DamonHolland/RubiksRobot/3D_Files/Final_3D_Files_Print_These/PS/PowerStruct.3mf

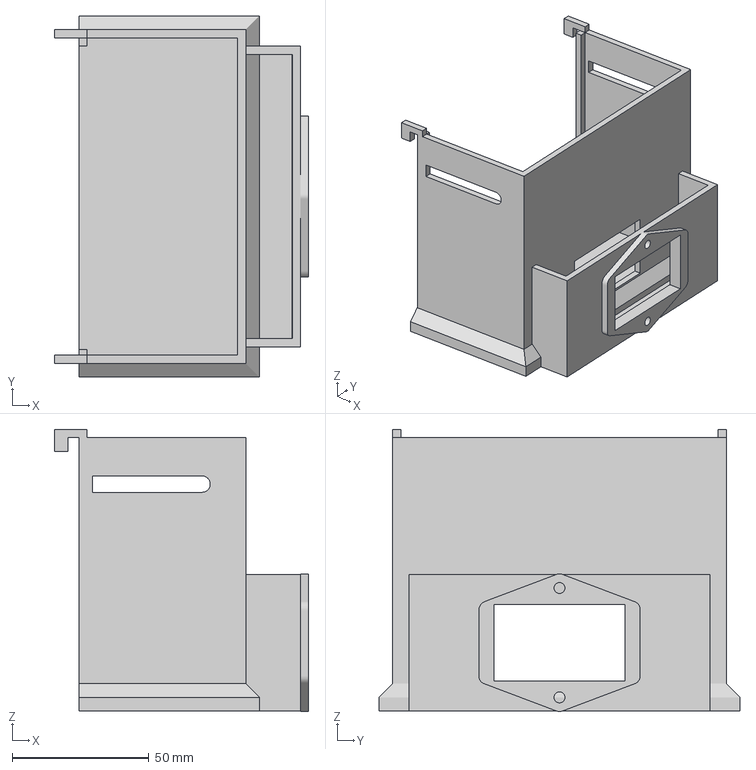
[picture p21: CAD file, 2022-01-24]
3D_Files/Final_3D_Files_Print_These/PS/PowerStruct.3mf
93.0 x 132.0 x 103.2 mm
