DamonHolland/RubiksRobot/3D_Files/NewArm/cubeThing.3mf

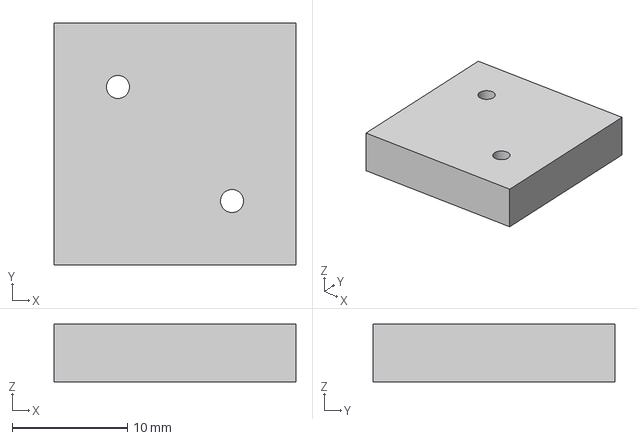
[picture p22: CAD file, 2022-01-30]
3D_Files/NewArm/cubeThing.3mf
21.0 x 21.0 x 5.00 mm
