DamonHolland/RubiksRobot/3D_Files/NewConnectors/BackConnector.3mf

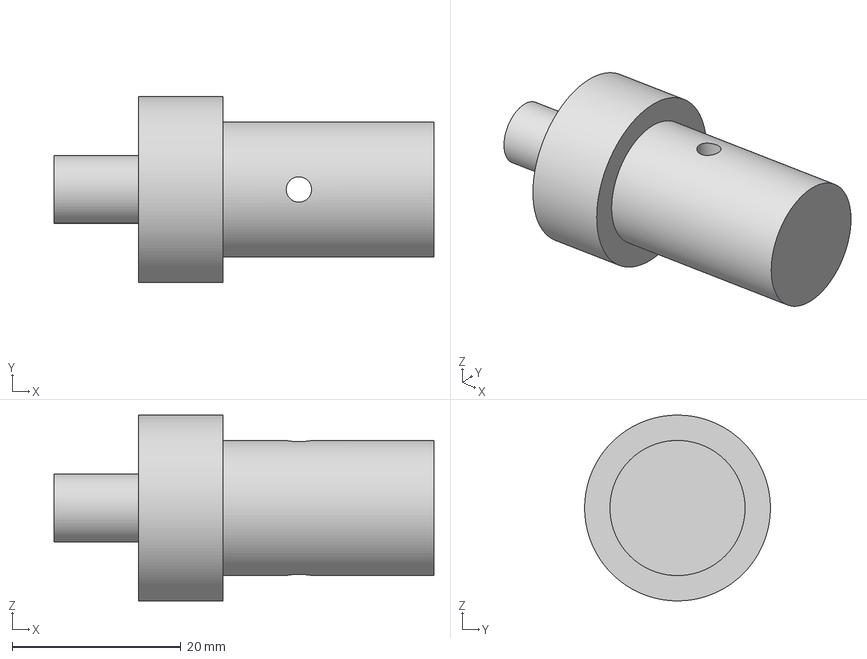
[picture p23: CAD file, 2021-12-20]
3D_Files/NewConnectors/BackConnector.3mf
45.0 x 22.0 x 22.0 mm
