DamonHolland/RubiksRobot/3D_Files/Structure/LowerHolder.3mf

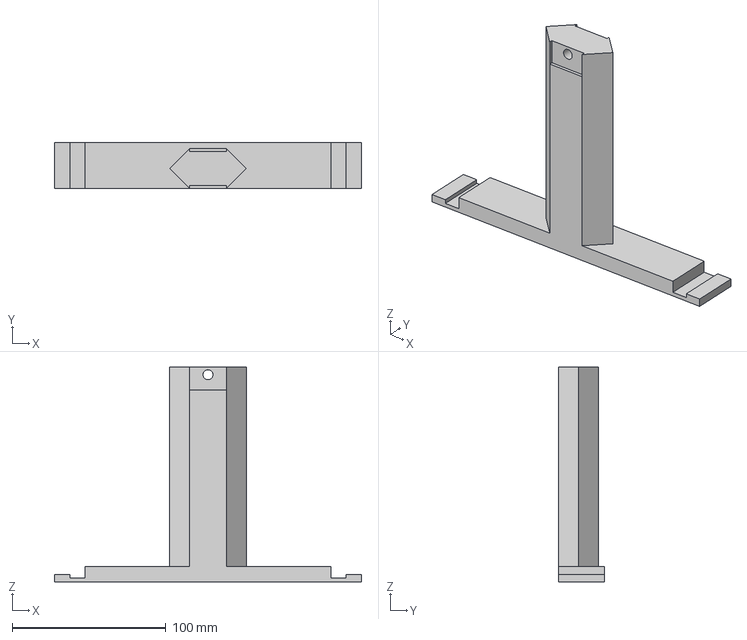
[picture p24: CAD file, 2021-11-13]
3D_Files/Structure/LowerHolder.3mf
200.0 x 30.0 x 140.0 mm
