DamonHolland/RubiksRobot/3D_Files/3DFiles/OutConnectorPin.3mf

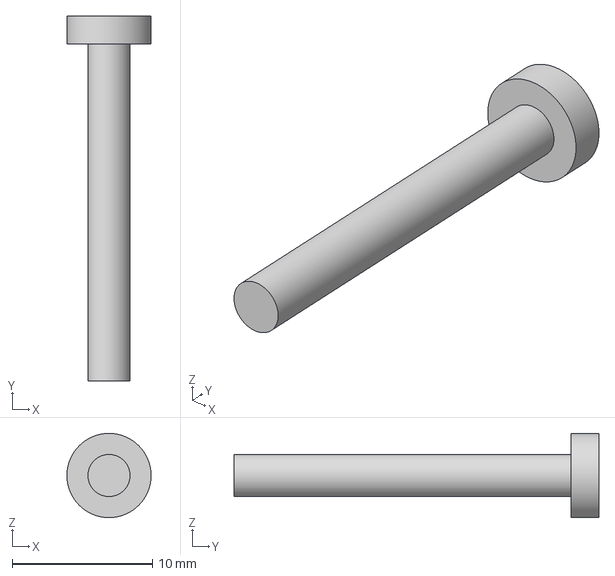
[picture p25: CAD file, 2021-11-19]
3D_Files/3DFiles/OutConnectorPin.3mf
6.00 x 26.0 x 6.00 mm
