DamonHolland/RubiksRobot/3D_Files/Final_3D_Files_Print_These/Arm/Outter.3mf

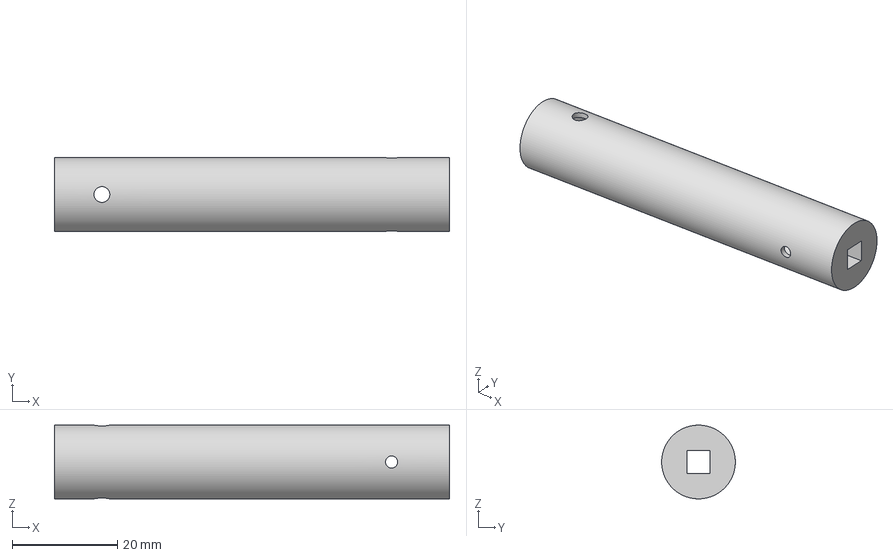
[picture p26: CAD file, 2022-01-17]
3D_Files/Final_3D_Files_Print_These/Arm/Outter.3mf
75.0 x 14.0 x 14.0 mm
