DamonHolland/RubiksRobot/3D_Files/Final_3D_Files_Print_These/BottomFrame/CornerLower.3mf

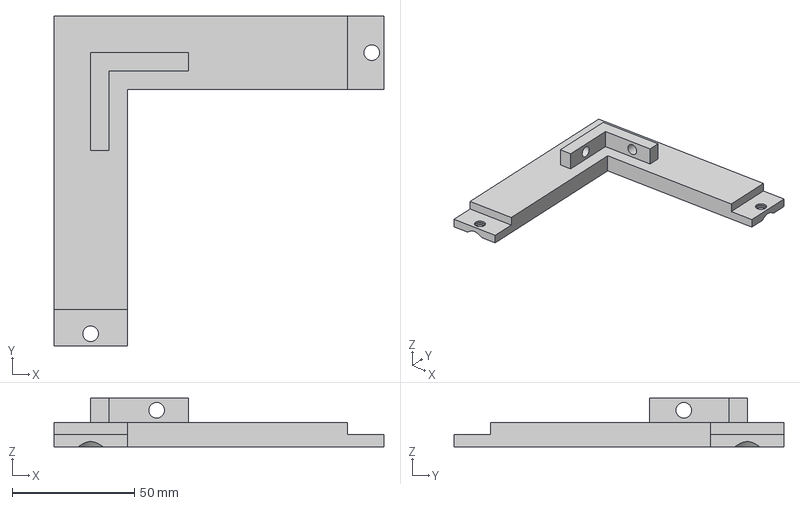
[picture p27: CAD file, 2021-12-20]
3D_Files/Final_3D_Files_Print_These/BottomFrame/CornerLower.3mf
135.0 x 135.0 x 20.0 mm
