DamonHolland/RubiksRobot/3D_Files/Final_3D_Files_Print_These/PS/DriverStruct.3mf

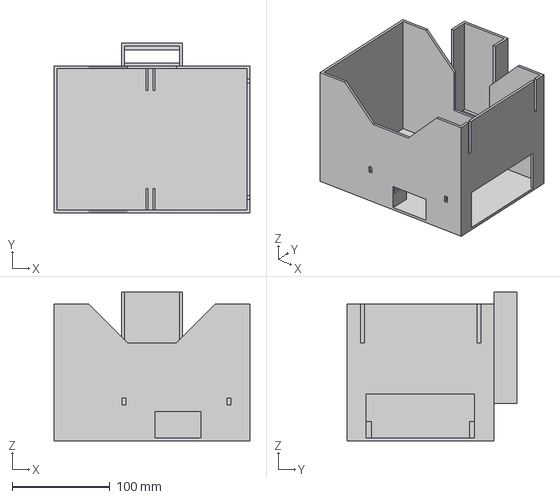
[picture p28: CAD file, 2022-01-08]
3D_Files/Final_3D_Files_Print_These/PS/DriverStruct.3mf
200.0 x 173.0 x 152.0 mm
