DamonHolland/RubiksRobot/3D_Files/Front_Arm.stl

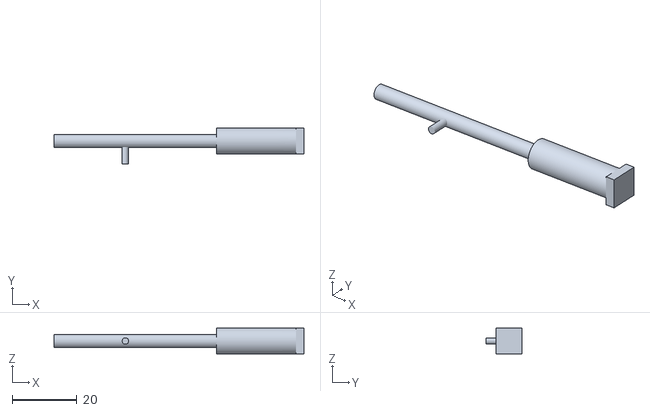
[picture p29: CAD file, 2021-11-13]
3D_Files/Front_Arm.stl
77.0 x 11.0 x 8.00
