DamonHolland/RubiksRobot/3D_Files/Structure/UpperHolder.3mf

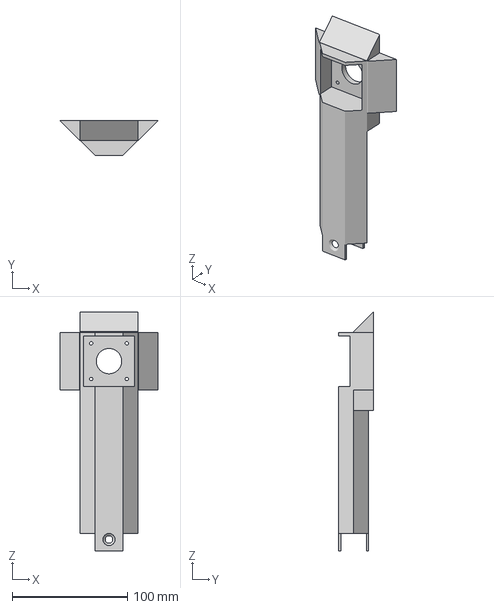
[picture p30: CAD file, 2021-11-13]
3D_Files/Structure/UpperHolder.3mf
85.4 x 30.0 x 207.7 mm
