DamonHolland/RubiksRobot/3D_Files/3DFiles/CleanConnector.3mf

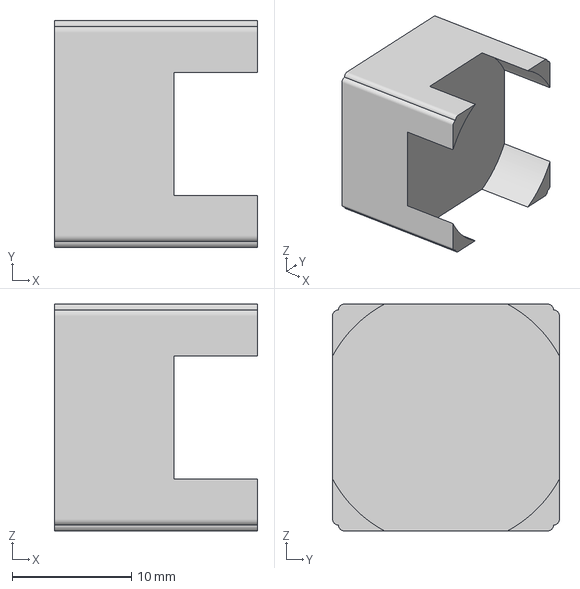
[picture p31: CAD file, 2021-11-17]
3D_Files/3DFiles/CleanConnector.3mf
17.0 x 19.0 x 19.0 mm
