DamonHolland/RubiksRobot/3D_Files/Final_3D_Files_Print_These/Arm/pin.3mf

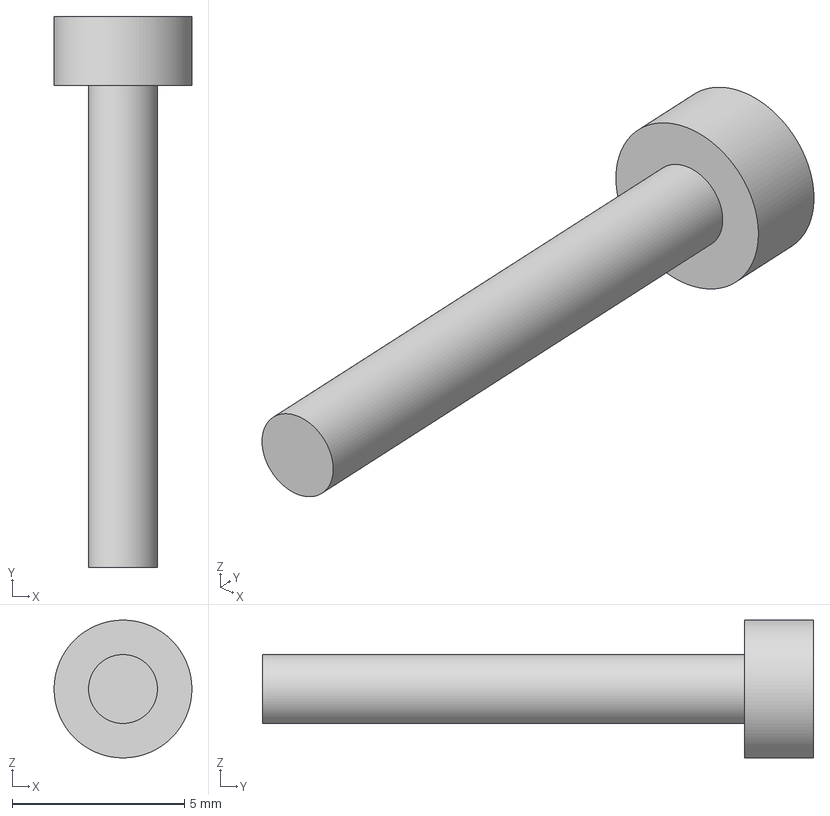
[picture p32: CAD file, 2022-01-17]
3D_Files/Final_3D_Files_Print_These/Arm/pin.3mf
4.00 x 16.0 x 4.00 mm
