DamonHolland/RubiksRobot/3D_Files/Final_3D_Files_Print_These/PS/WireStruct.3mf

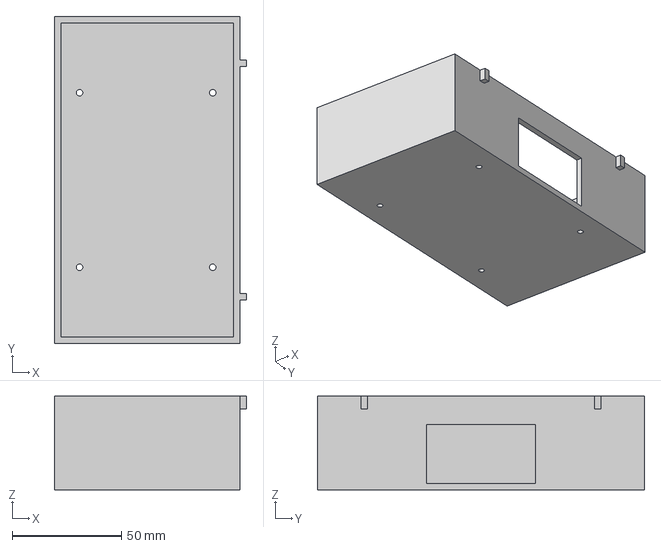
[picture p33: CAD file, 2022-01-08]
3D_Files/Final_3D_Files_Print_These/PS/WireStruct.3mf
88.0 x 150.0 x 43.0 mm
