DamonHolland/RubiksRobot/3D_Files/Structure/CorrectPin.3mf

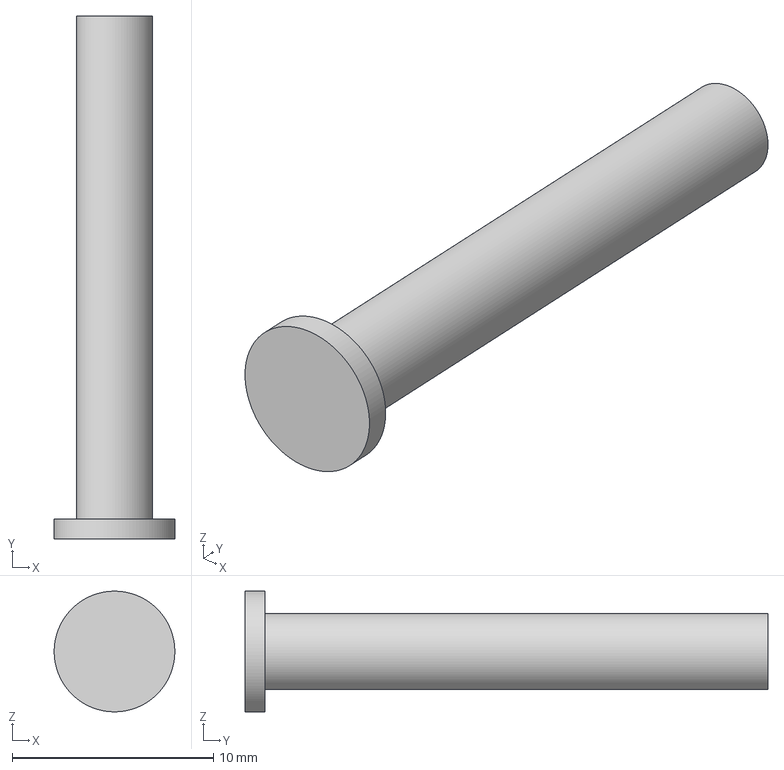
[picture p34: CAD file, 2021-11-13]
3D_Files/Structure/CorrectPin.3mf
6.00 x 26.0 x 6.00 mm
