DamonHolland/RubiksRobot/3D_Files/3DFiles/InnerConnectorHole.3mf

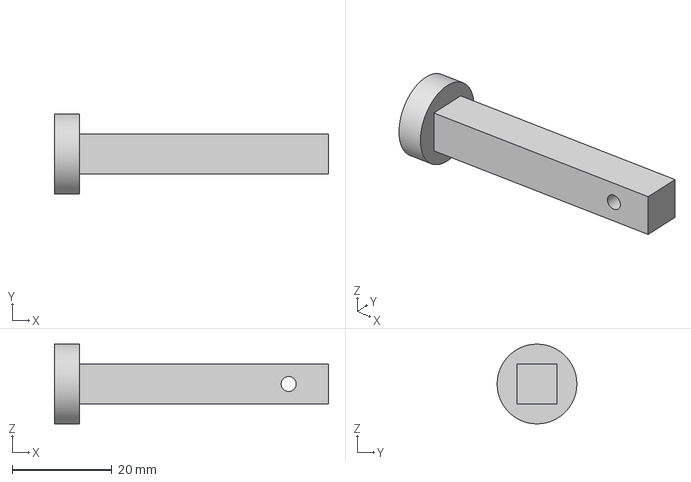
[picture p35: CAD file, 2021-11-16]
3D_Files/3DFiles/InnerConnectorHole.3mf
55.0 x 16.0 x 16.0 mm
