DamonHolland/RubiksRobot/3D_Files/Final_3D_Files_Print_These/Arm/Back.3mf

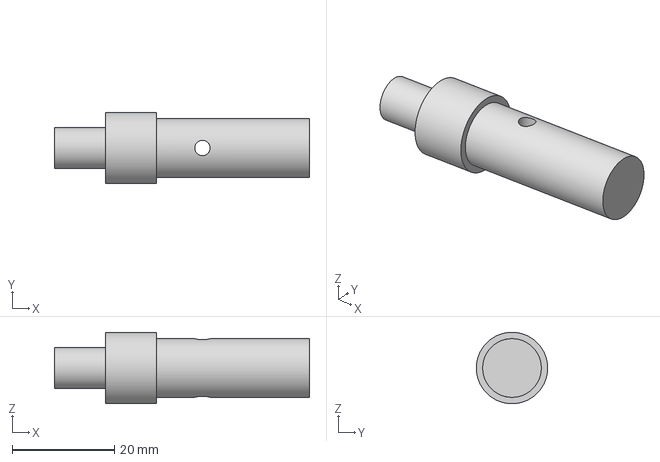
[picture p36: CAD file, 2022-01-17]
3D_Files/Final_3D_Files_Print_These/Arm/Back.3mf
50.0 x 14.0 x 14.0 mm
