DamonHolland/RubiksRobot/3D_Files/Final_3D_Files_Print_These/BottomFrame/BottomStructure.3mf

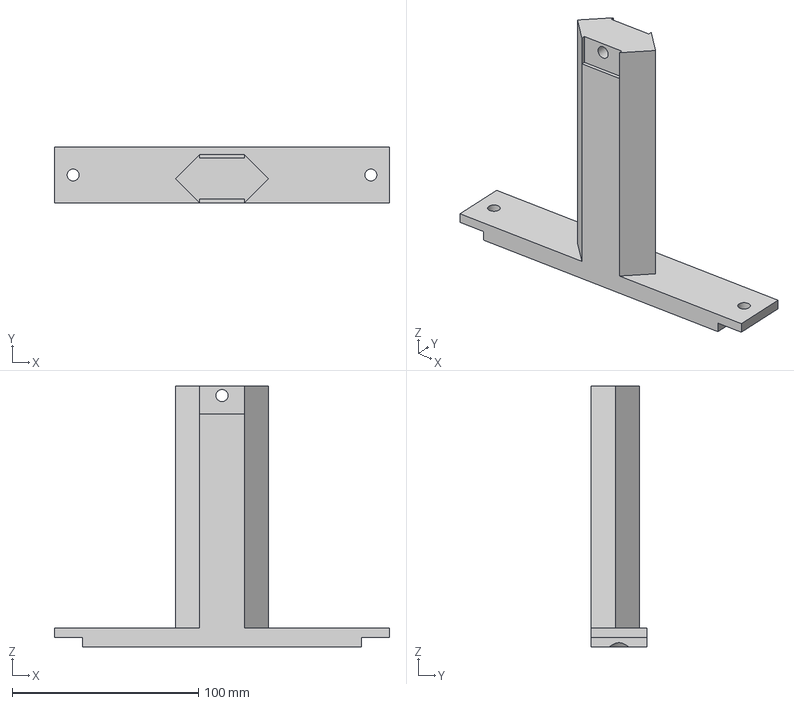
[picture p37: CAD file, 2021-11-13]
3D_Files/Final_3D_Files_Print_These/BottomFrame/BottomStructure.3mf
180.0 x 30.0 x 140.0 mm
