DamonHolland/RubiksRobot/3D_Files/Final_3D_Files_Print_These/CircleFrame/SideCircle2.3mf

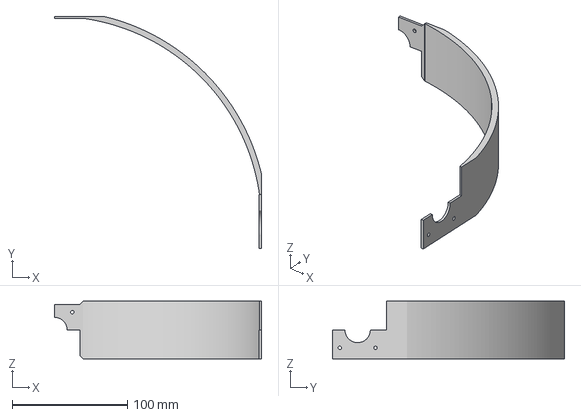
[picture p38: CAD file, 2021-11-13]
3D_Files/Final_3D_Files_Print_These/CircleFrame/SideCircle2.3mf
180.0 x 202.0 x 50.0 mm
