DamonHolland/RubiksRobot/3D_Files/Final_3D_Files_Print_These/PS/handle.3mf

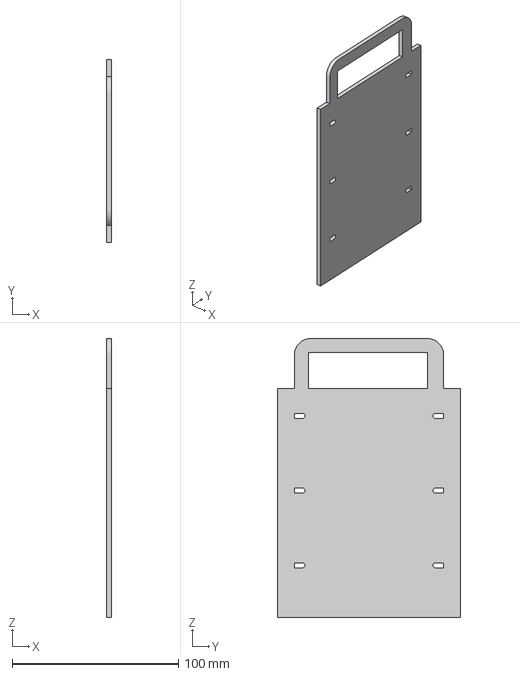
[picture p39: CAD file, 2022-01-05]
3D_Files/Final_3D_Files_Print_These/PS/handle.3mf
3.00 x 110.0 x 168.0 mm
