DamonHolland/RubiksRobot/3D_Files/3DFiles/FinalConnectorLong.3mf

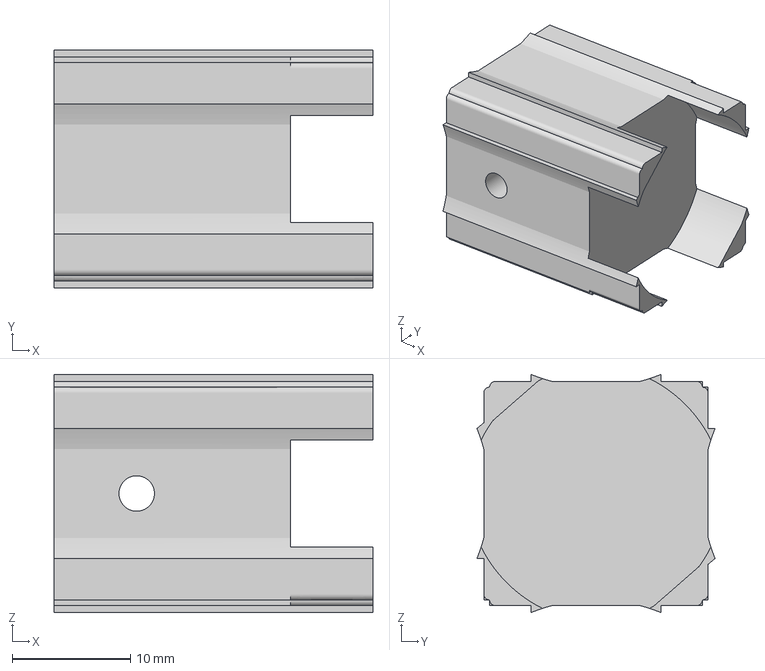
[picture p40: CAD file, 2021-11-16]
3D_Files/3DFiles/FinalConnectorLong.3mf
27.0 x 20.2 x 20.2 mm
