DamonHolland/RubiksRobot/3D_Files/Final_3D_Files_Print_These/BottomFrame/2ConnectorTop.3mf

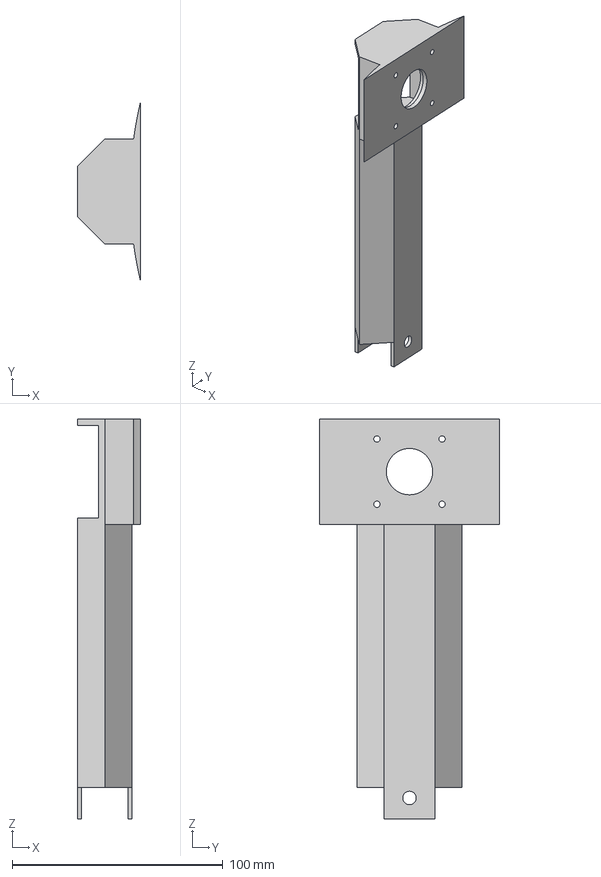
[picture p41: CAD file, 2021-11-13]
3D_Files/Final_3D_Files_Print_These/BottomFrame/2ConnectorTop.3mf
30.0 x 85.4 x 190.0 mm
