DamonHolland/RubiksRobot/3D_Files/3DFiles/FinalConnectorBest.3mf

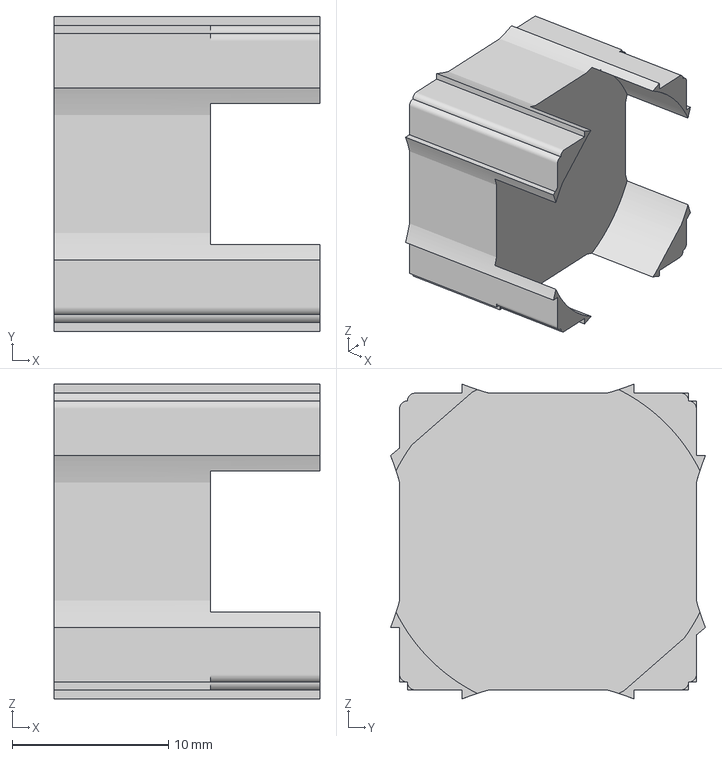
[picture p42: CAD file, 2021-11-16]
3D_Files/3DFiles/FinalConnectorBest.3mf
17.0 x 20.2 x 20.2 mm
