DamonHolland/RubiksRobot/3D_Files/Final_3D_Files_Print_These/BottomFrame/CornerLowerNoConnector.3mf

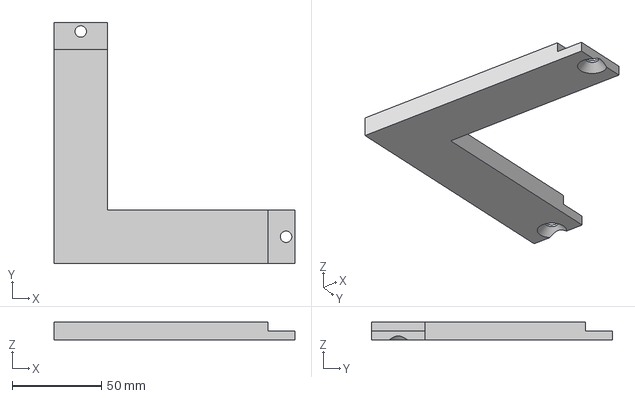
[picture p43: CAD file, 2021-11-13]
3D_Files/Final_3D_Files_Print_These/BottomFrame/CornerLowerNoConnector.3mf
135.0 x 135.0 x 10.0 mm
