DamonHolland/RubiksRobot/3D_Files/3DFiles/BigFinalConnector.3mf

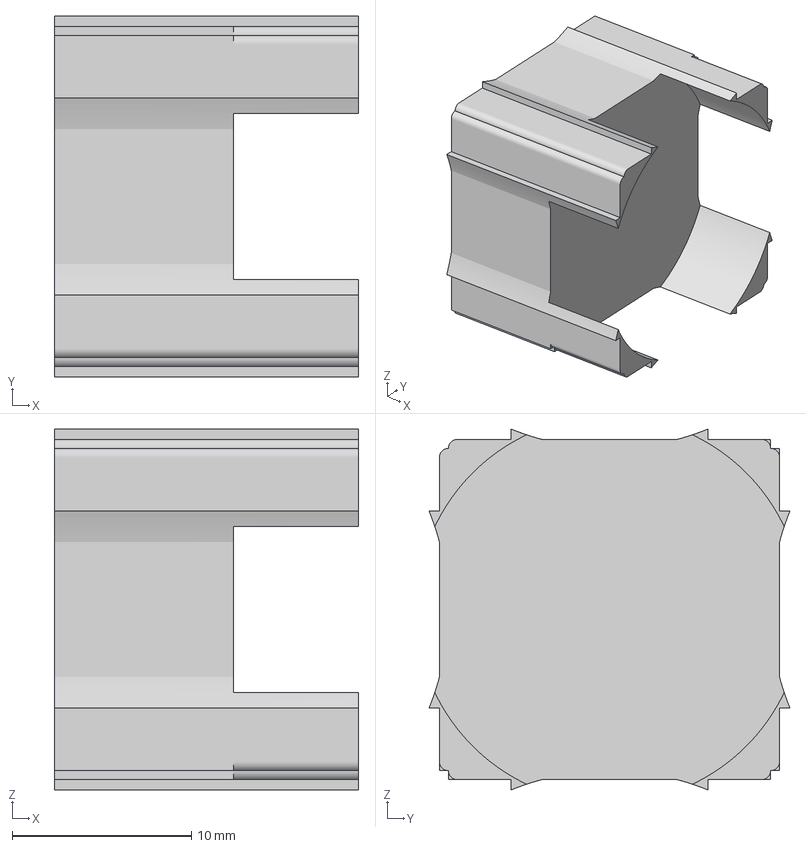
[picture p44: CAD file, 2021-11-15]
3D_Files/3DFiles/BigFinalConnector.3mf
17.0 x 20.2 x 20.2 mm
