DamonHolland/RubiksRobot/3D_Files/3DFiles/TallCamMiddle.3mf

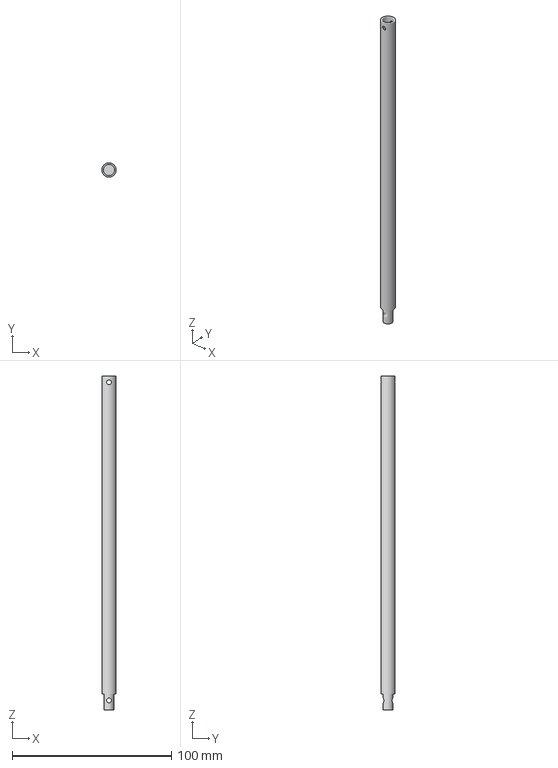
[picture p45: CAD file, 2021-11-14]
3D_Files/3DFiles/TallCamMiddle.3mf
9.00 x 9.00 x 210.0 mm
