DamonHolland/RubiksRobot/3D_Files/3DFiles/TallCamLower.3mf

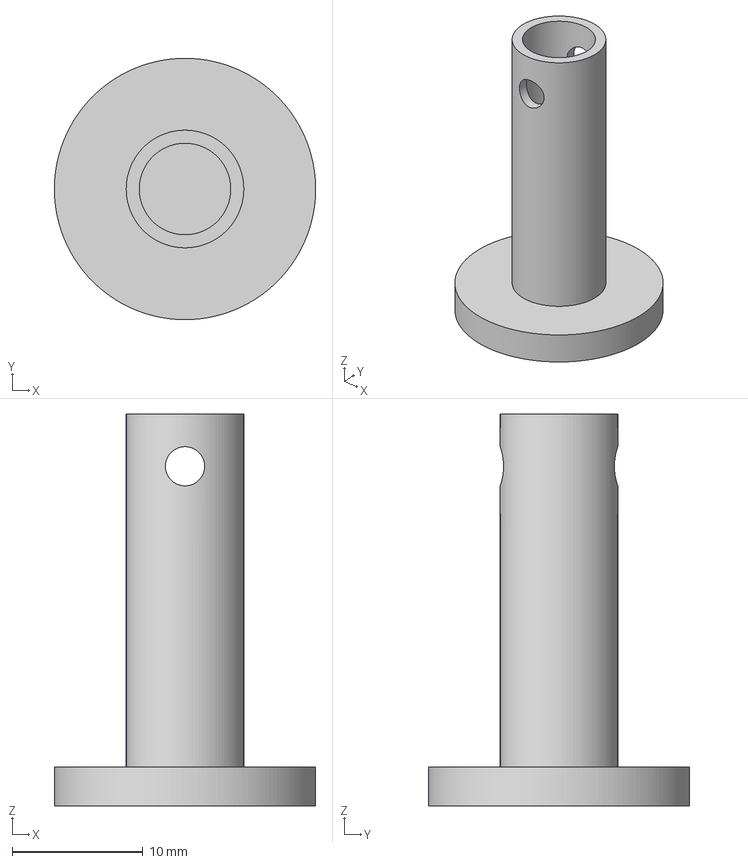
[picture p46: CAD file, 2021-11-14]
3D_Files/3DFiles/TallCamLower.3mf
20.0 x 20.0 x 30.0 mm
