DamonHolland/RubiksRobot/3D_Files/3DFiles/TallCamUpper.3mf

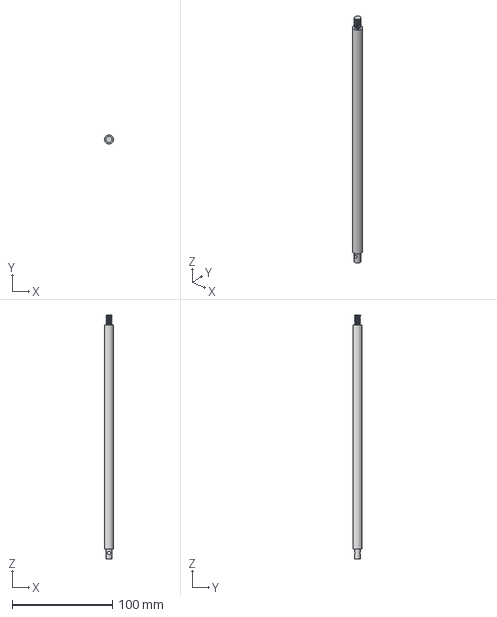
[picture p47: CAD file, 2021-11-13]
3D_Files/3DFiles/TallCamUpper.3mf
8.99 x 8.99 x 243.0 mm
