DamonHolland/RubiksRobot/3D_Files/3DFiles/NewCornerWithHole.3mf

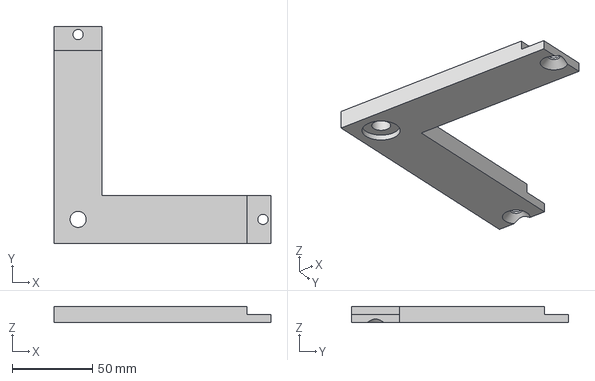
[picture p48: CAD file, 2021-11-13]
3D_Files/3DFiles/NewCornerWithHole.3mf
135.0 x 135.0 x 10.0 mm
