DamonHolland/RubiksRobot/3D_Files/3DFiles/NewBackConnector.3mf

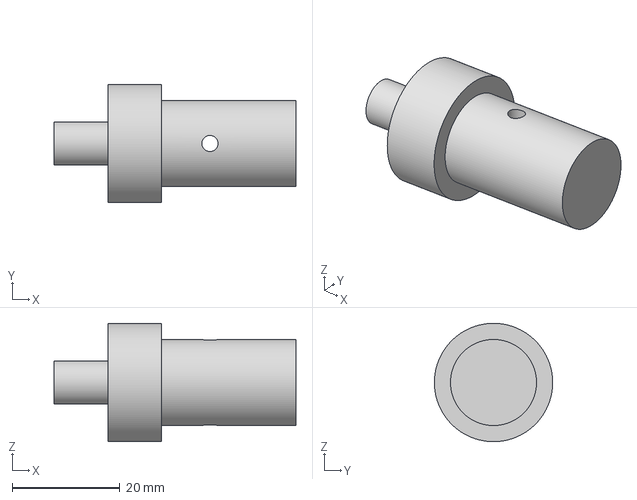
[picture p49: CAD file, 2021-11-13]
3D_Files/3DFiles/NewBackConnector.3mf
45.0 x 22.0 x 22.0 mm
