DamonHolland/RubiksRobot/3D_Files/3DFiles/PillarSmall.3mf

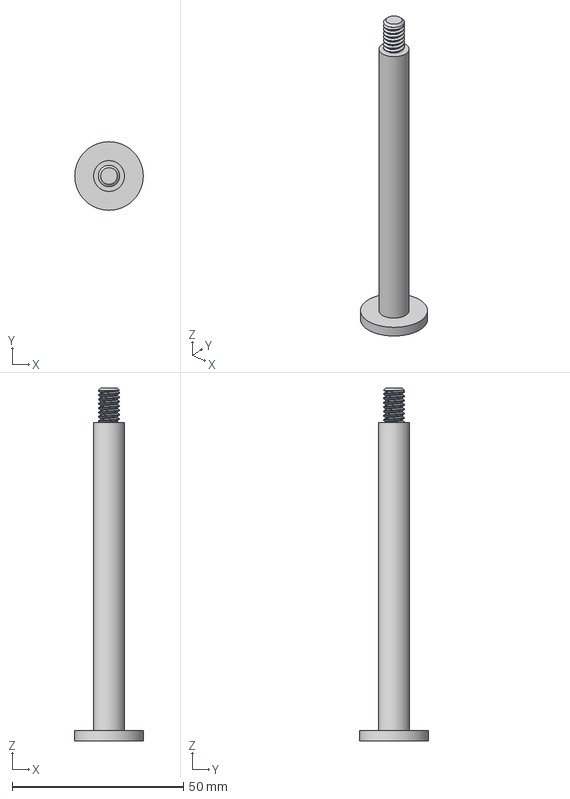
[picture p50: CAD file, 2021-11-13]
3D_Files/3DFiles/PillarSmall.3mf
20.0 x 20.0 x 103.0 mm
