DamonHolland/RubiksRobot/3D_Files/3DFiles/NewestConnector.3mf

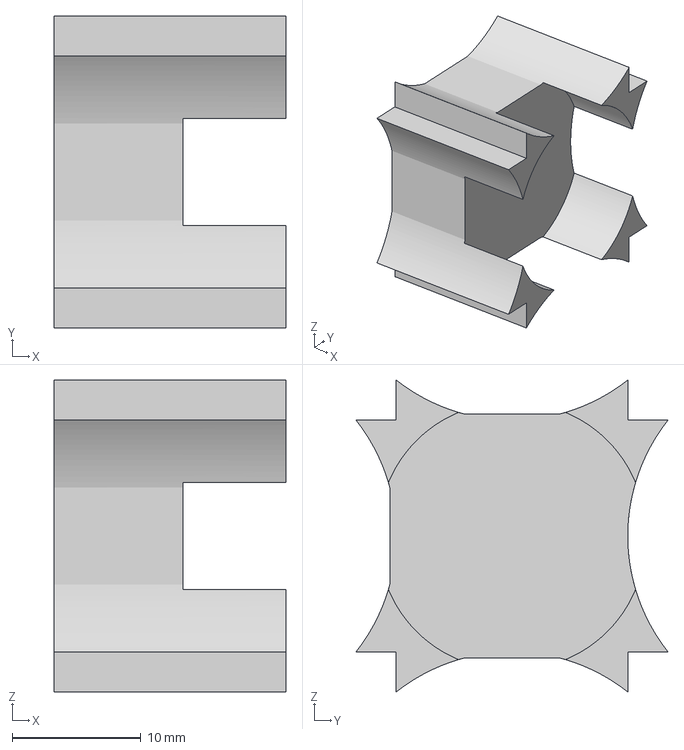
[picture p51: CAD file, 2021-11-13]
3D_Files/3DFiles/NewestConnector.3mf
18.0 x 24.3 x 24.3 mm
