DamonHolland/RubiksRobot/3D_Files/3DFiles/NewConnector.3mf

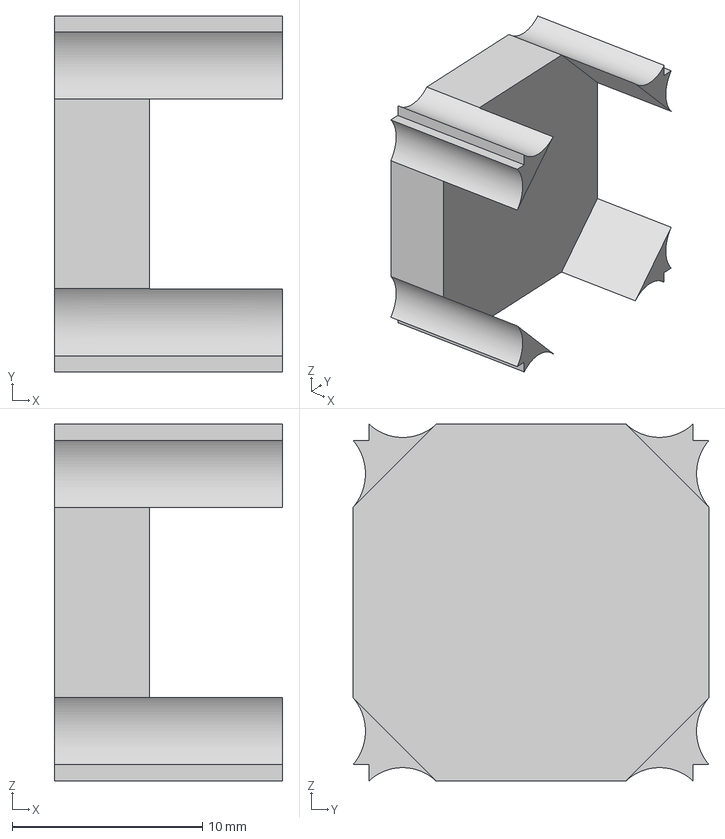
[picture p52: CAD file, 2021-11-13]
3D_Files/3DFiles/NewConnector.3mf
12.0 x 18.7 x 18.7 mm
